doesntfazer/Goober/Goobertrax/3d Models - Case files/Trackball Holder - Click-in.stl

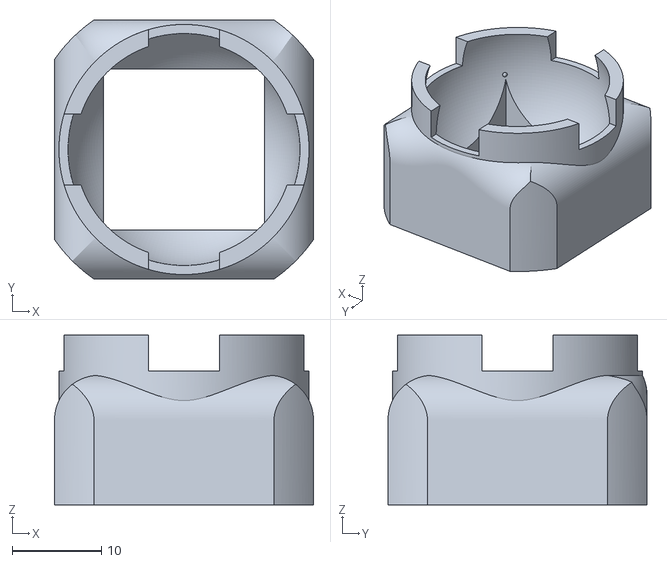
[picture p19: CAD file, 2024-09-03]
Goobertrax/3d Models - Case files/Trackball Holder - Click-in.stl
29.0 x 29.0 x 19.0
