doesntfazer/Goober/goober-CHOC/dxf/goober-wi-B_Cu.dxf

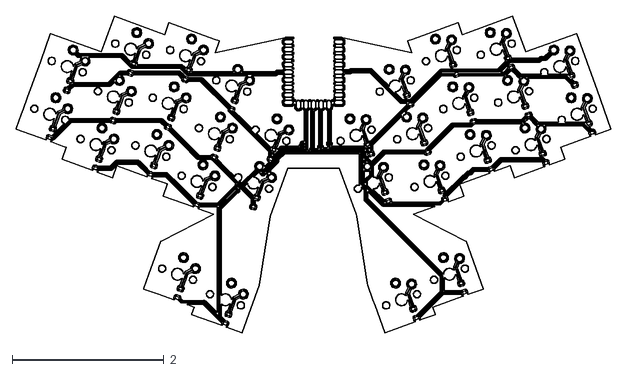
[picture p20: CAD file, 2024-09-03]
goober-CHOC/dxf/goober-wi-B_Cu.dxf
7.84 x 4.17
