doesntfazer/Goober/Goobertrax/3d Models - Case files/Plate.stl

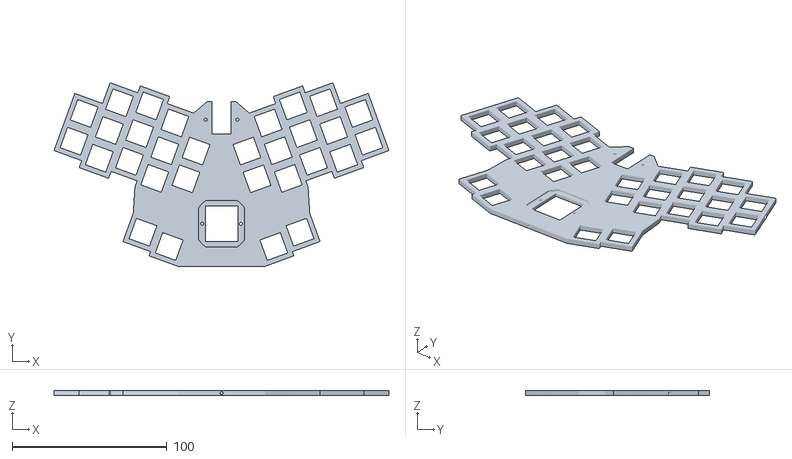
[picture p21: CAD file, 2024-09-03]
Goobertrax/3d Models - Case files/Plate.stl
216.3 x 118.5 x 3.00
