doesntfazer/Goober/Goobertrax/3d Models - Case files/Case.stl

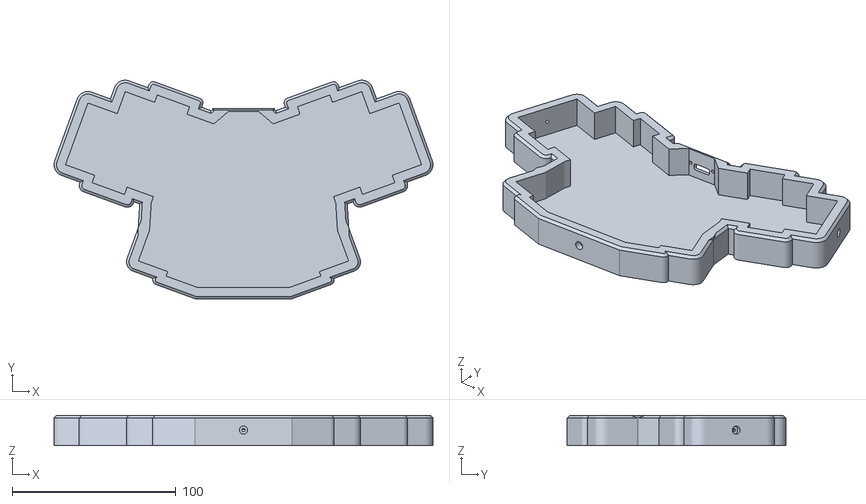
[picture p22: CAD file, 2024-09-03]
Goobertrax/3d Models - Case files/Case.stl
231.3 x 133.4 x 18.5
